MouseBiteFever/Pow-OR/fpf1320/power mux-fpf1320.brd

## EAGLE design fpf1320/power mux-fpf1320.brd (2014-05-03)

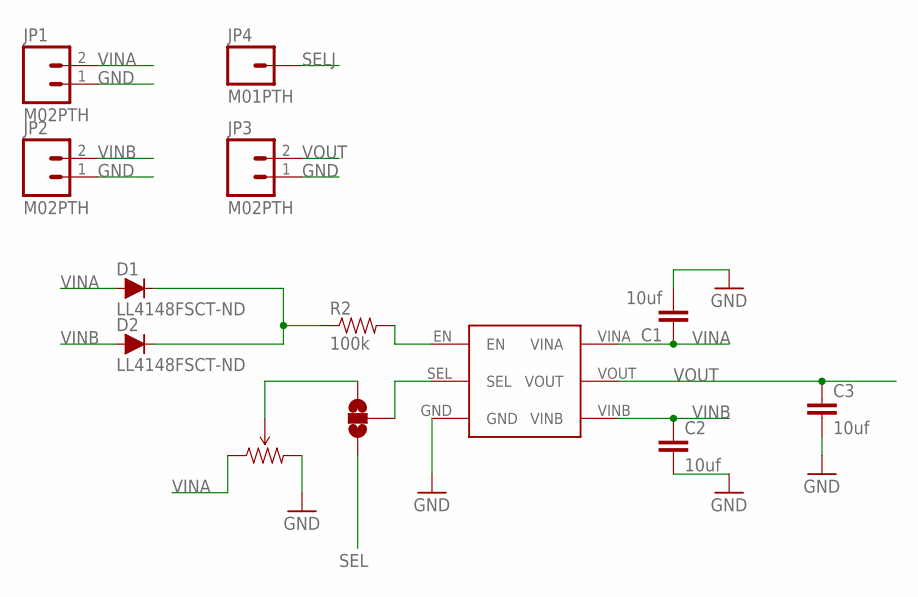
[picture p25: schematic power mux-fpf1320.sch]

Parts:
C1, C2, C3: 10uf; 0805
D1, D2: LL4148FSCT-ND; SOD80
JP1, JP2, JP3: M02PTH; 1X02
JP4: M01PTH; 1X01
R1: TRIMPOT-PTH-KNOB; 3386U
R2: 100k; 0805
SJ2: SOLDERJUMPER_2WAYPASTE1&2; SJ_3_PASTE1&2
U$3: FPF1320; 6-UFBGA

Connections:
GND: C1.2, C2.2, C3.2, JP1.1, JP2.1, JP3.1, R1.3 (CW), U$3.GND
unnamed: D1.1 (C), D2.1 (C), R2.1
unnamed: R2.2, U$3.EN
unnamed: SJ2.2, U$3.SEL
SEL: R1.2 (WIPER), SJ2.3
SELJ: JP4.1, SJ2.1
VINA: C1.1, D1.2 (A), JP1.2, R1.1 (CCW), U$3.VINA
VINB: C2.1, D2.2 (A), JP2.2, U$3.VINB
VOUT: C3.1, JP3.2, U$3.VOUT

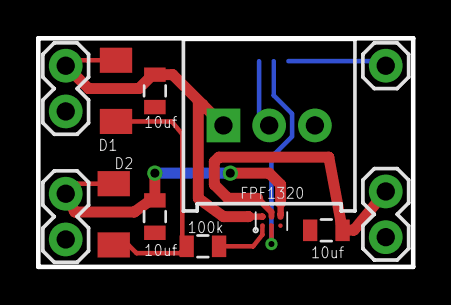
[picture p26: board power mux-fpf1320.brd from above]

Board: 2 copper layers, 20.8 x 12.7 mm, 13 parts (1 on the bottom side), 9 nets.
